openxc/smart-wiper/Android/ConnectedWiper/ic_launcher-web.png

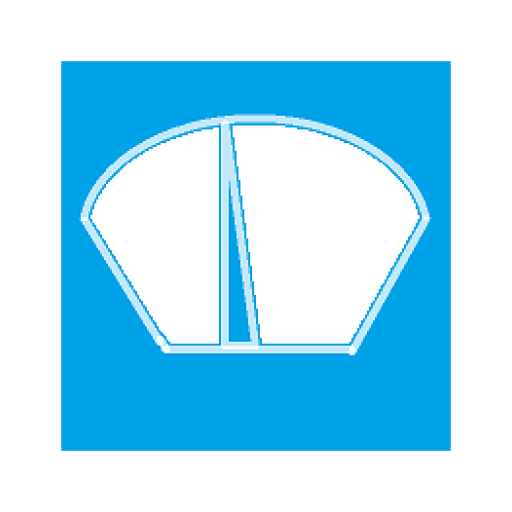
Android/ConnectedWiper/ic_launcher-web.png
