openxc/smart-wiper/CAD/BOX_ver2.png

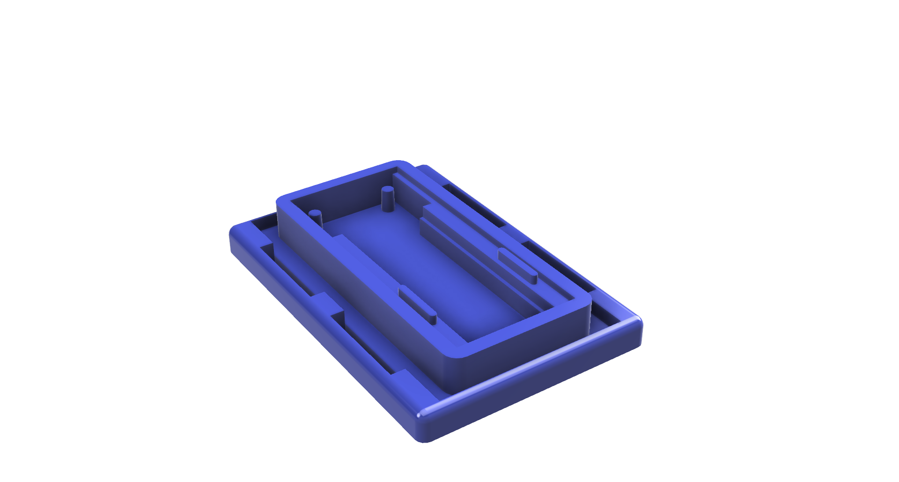
CAD/BOX_ver2.png
