openxc/smart-wiper/CAD/INSERT_ver2.png

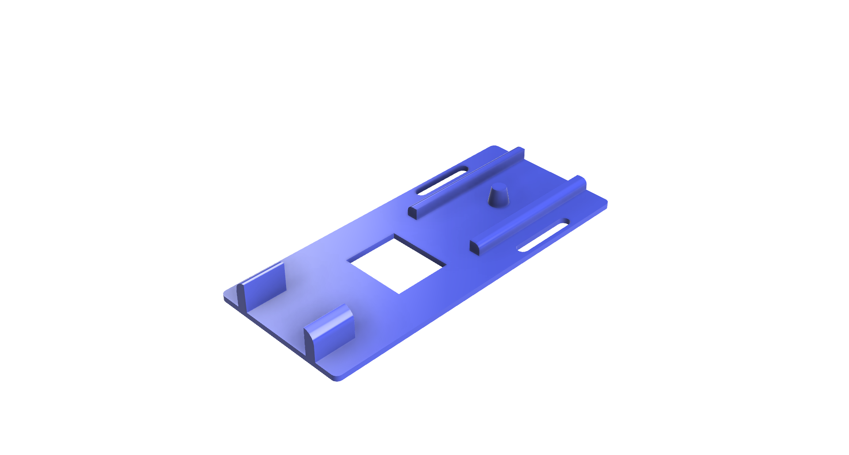
CAD/INSERT_ver2.png
