openxc/smart-wiper/CAD/LID_ver2.png

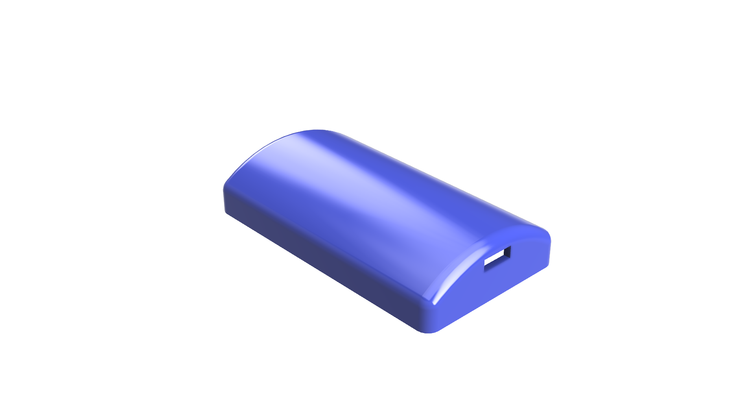
CAD/LID_ver2.png
