openxc/smart-wiper/Docs/android.png

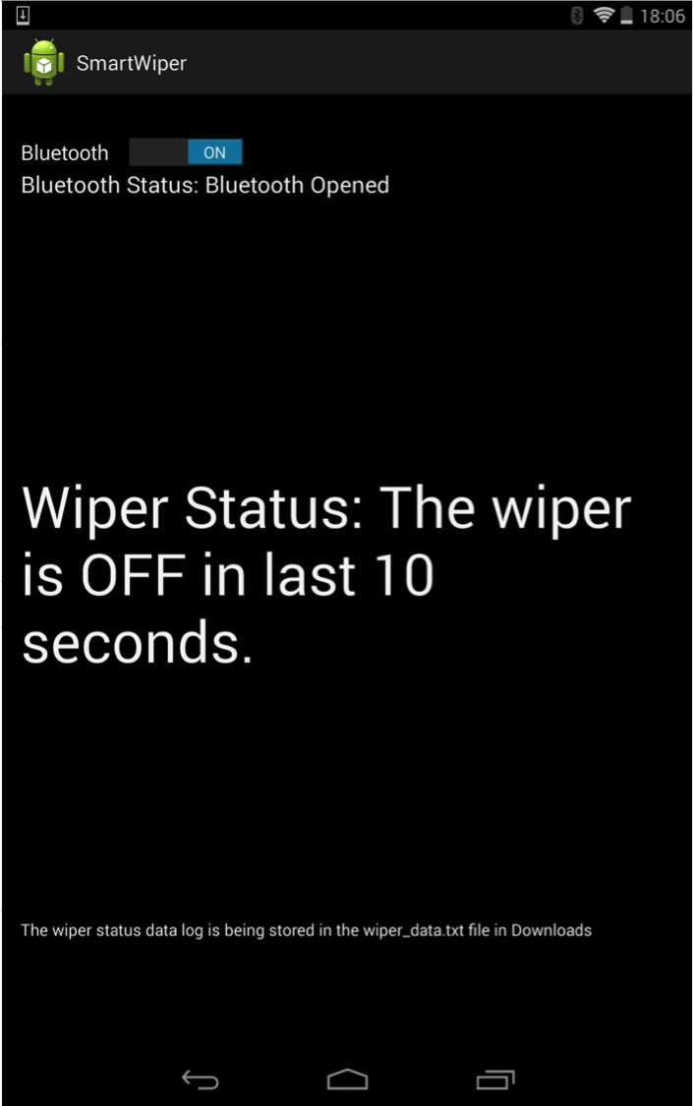
Docs/android.png
