openxc/smart-wiper/Docs/enclosure.JPG

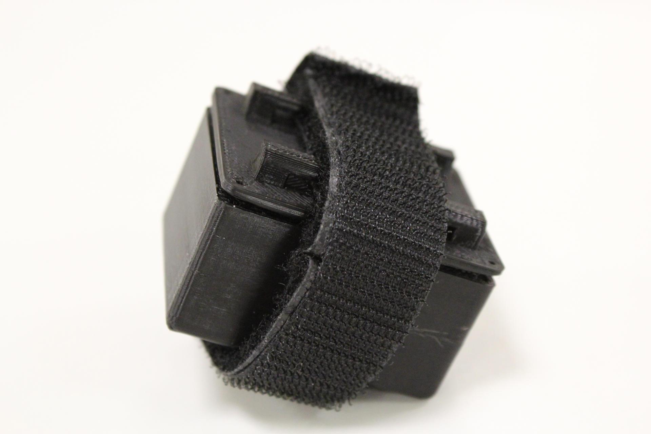
Docs/enclosure.JPG
