openxc/smart-wiper/Docs/SmartWiper_bb.png

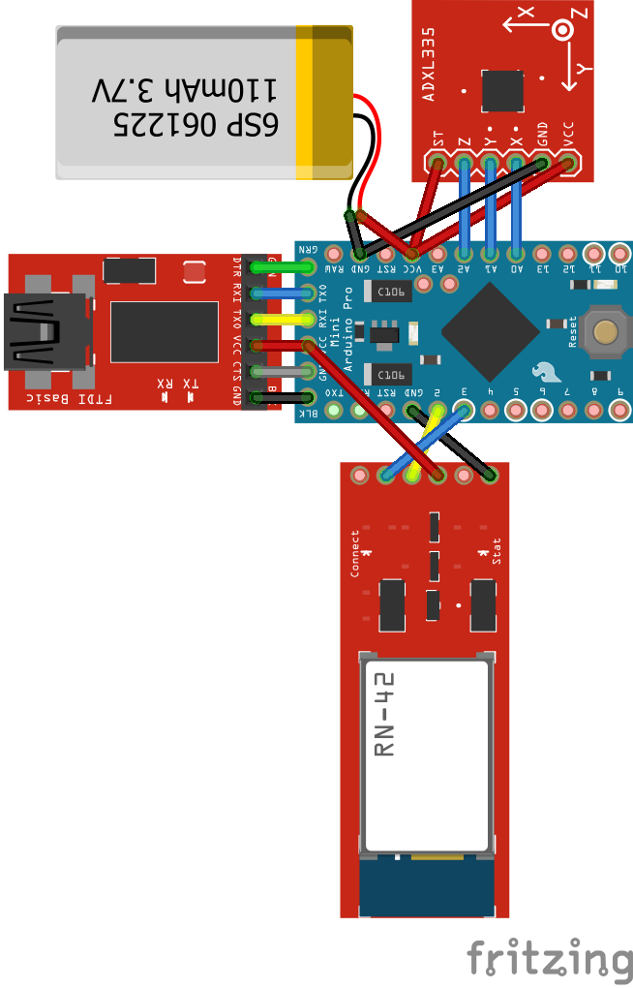
Docs/SmartWiper_bb.png
