openxc/smart-wiper/Docs/smartwiperbox.JPG

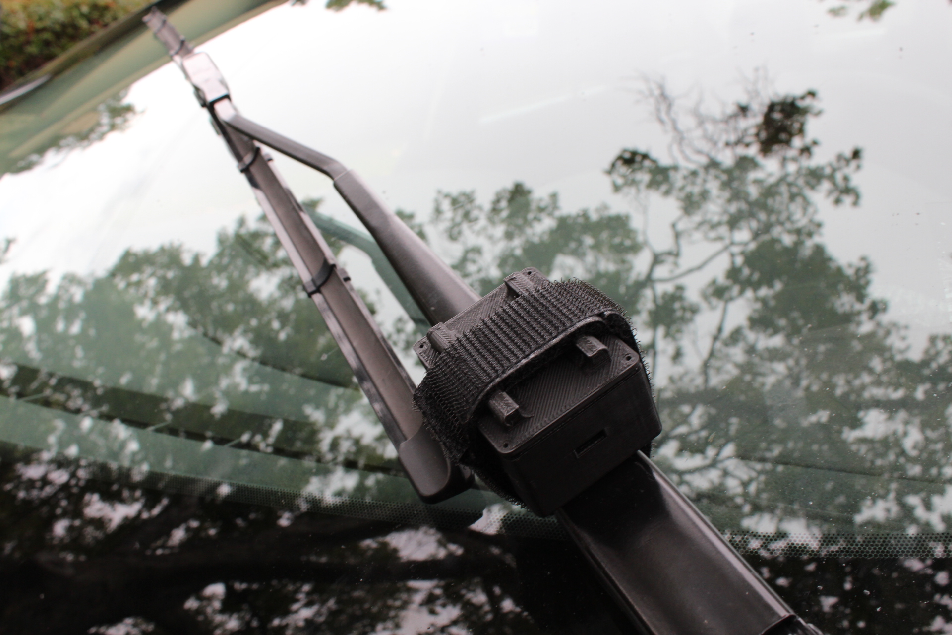
Docs/smartwiperbox.JPG
