openxc/smart-wiper/Docs/usb.jpg

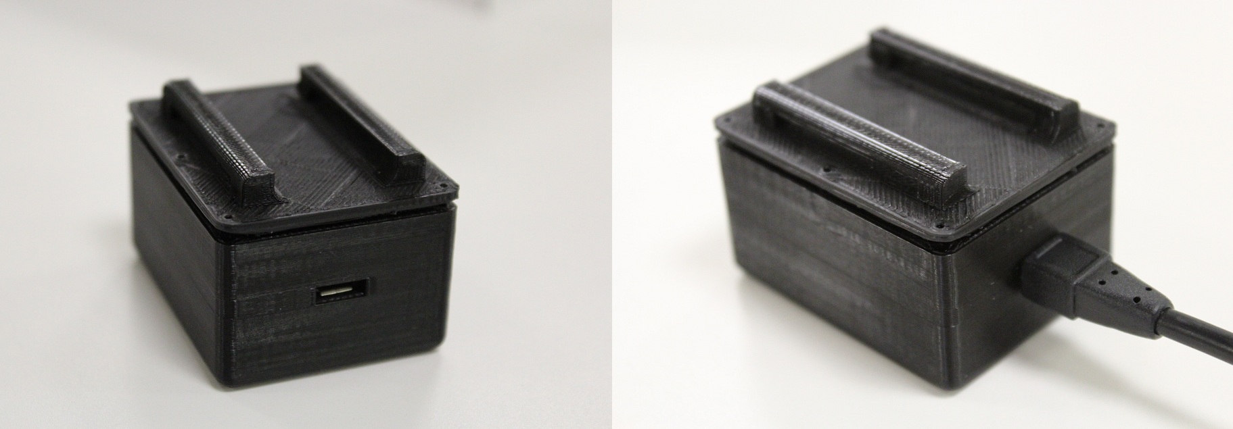
Docs/usb.jpg
